machdyne/minze/rtl/blinky_minze.v

// MINZE BLINKY

module blinky #()
(

	input CLK_48,

	output LED_A,

);

	reg [28:0] counter = 0;

   assign LED_A = ~counter[25];

   always @(posedge CLK_48) begin
      counter <= counter + 1;
   end

endmodule
